EDA-bench/eda-bench/artifacts/first5_gold/bq24074_usb_c_lipo.png

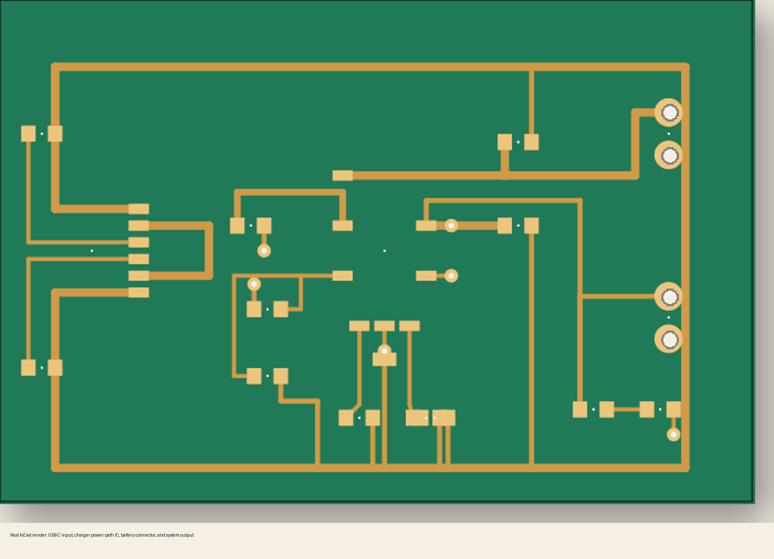
artifacts/first5_gold/bq24074_usb_c_lipo.png
