EDA-bench/eda-bench/artifacts/first5_gold/can_fd_tcan1051.png

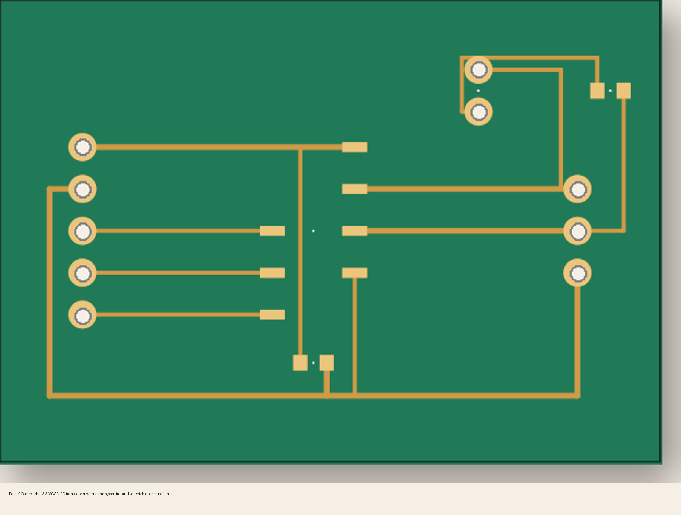
artifacts/first5_gold/can_fd_tcan1051.png
