EDA-bench/eda-bench/artifacts/first5_gold/usb_c_5v_sink_protected_iso3d.png

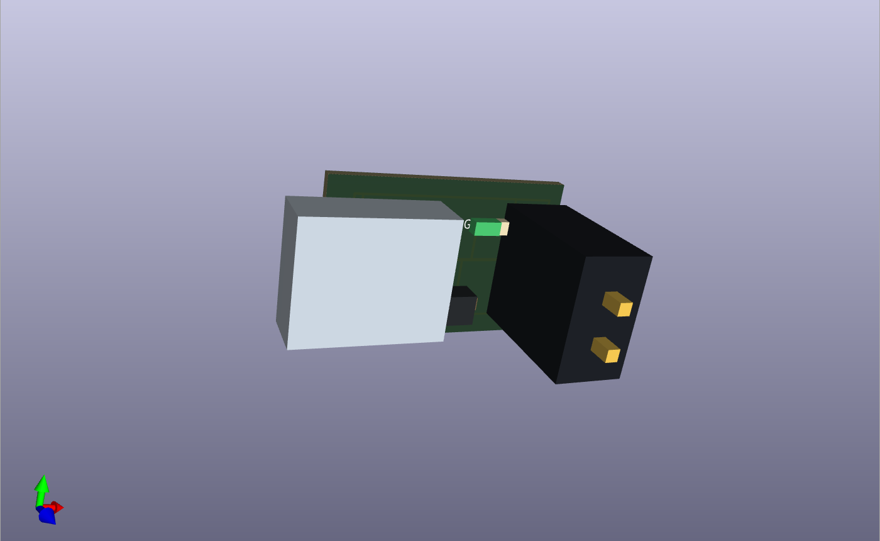
artifacts/first5_gold/usb_c_5v_sink_protected_iso3d.png
